Ninjadude01/Ninjaboard65/Pictures/IMG_5813.jpg

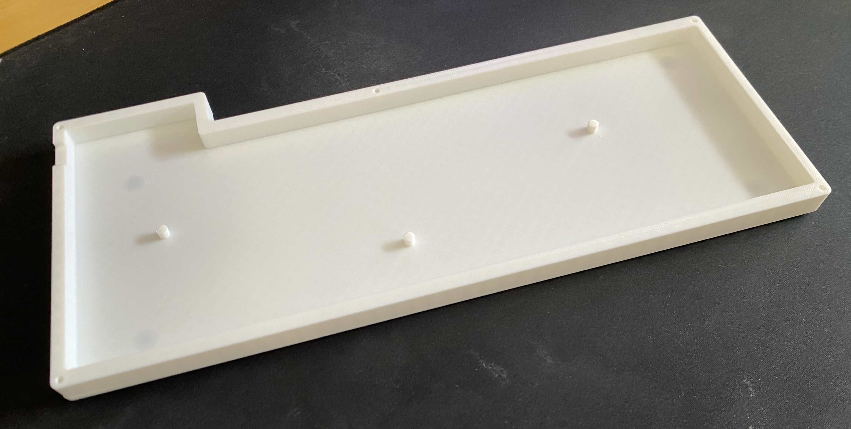
Pictures/IMG_5813.jpg
