Ninjadude01/Ninjaboard65/Pictures/IMG_5814.jpg

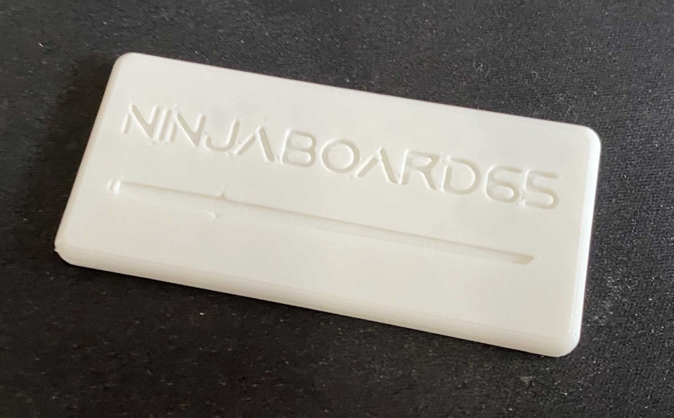
Pictures/IMG_5814.jpg
